DE41H/self-balancing-robot/hardware/schematic/self-balancing-robot/self-balancing-robot.kicad_pcb

## KiCad design Electronic_load_esp32/Electronic_load_esp32.kicad_sch

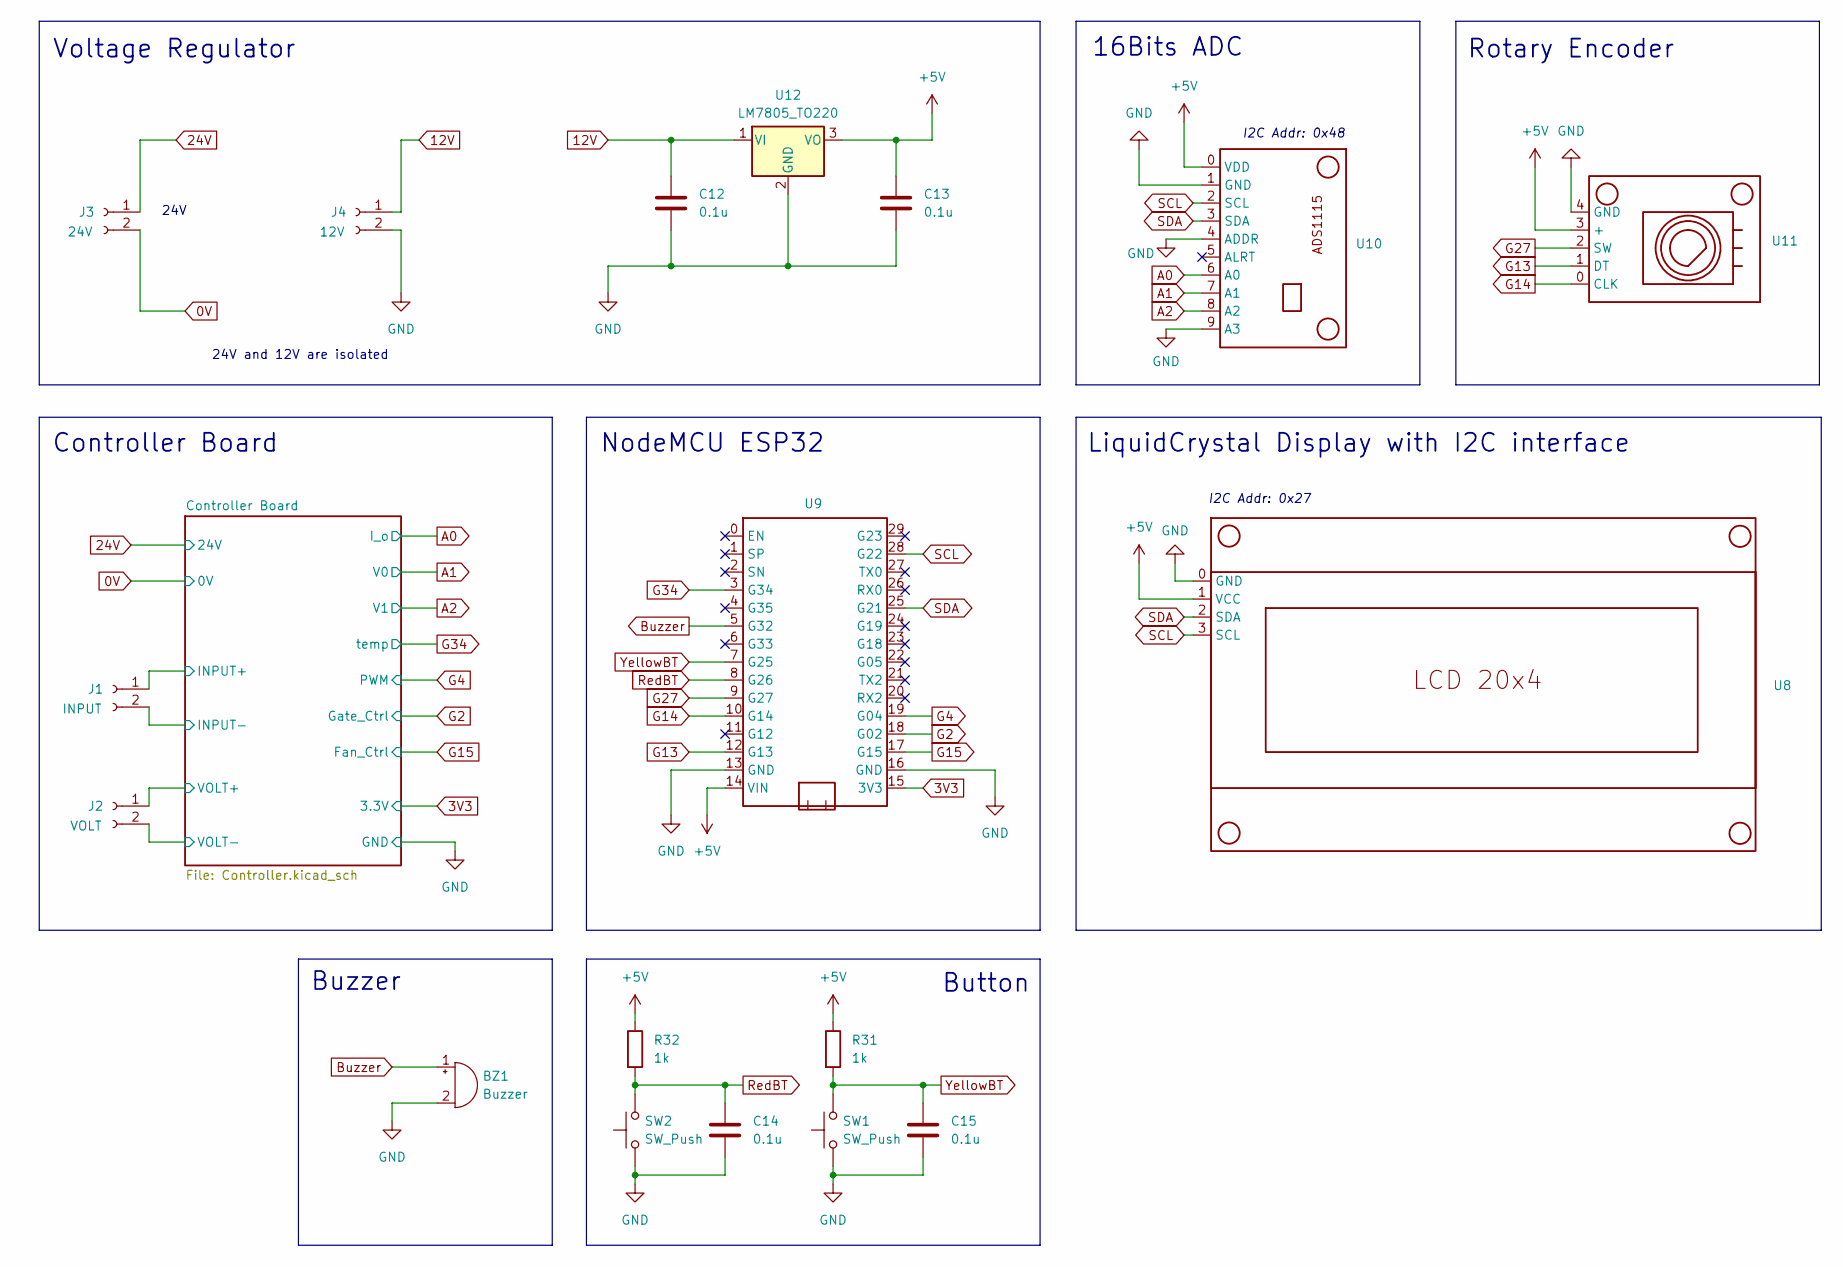
[picture p3: schematic Electronic_load_esp32.kicad_sch]

Parts:
BZ1: Buzzer
C12, C13, C14, C15: 0.1u
J1: INPUT; JST_XA_B02B-XASK-1_1x02_P2.50mm_Vertical
J2: VOLT; JST_XA_B02B-XASK-1_1x02_P2.50mm_Vertical
J3: 24V; JST_XA_B02B-XASK-1_1x02_P2.50mm_Vertical
J4: 12V; JST_XA_B02B-XASK-1_1x02_P2.50mm_Vertical
R31, R32: 1k
SW1, SW2: SW_Push
U8, U10, U11: (no value)
U9: NodeMCU_ESP32_30PIN
U12: LM7805_TO220; TO-220-3_Vertical

Connections:
0V: J3.2
3V3: U9.15 (3V3)
12V: C12.1, J4.1, U12.1 (VI)
24V: J3.1
+5V: C13.1, R31.1, R32.1, U8.1 (VCC), U9.14 (VIN), U10.0 (VDD), U11.3 (+), U12.3 (VO)
A0: U10.6 (A0)
A1: U10.7 (A1)
A2: U10.8 (A2)
Buzzer: BZ1.1 (+), U9.5 (G32)
G2: U9.18 (G02)
G4: U9.19 (G04)
G13: U9.12 (G13), U11.1 (DT)
G14: U9.10 (G14), U11.0 (CLK)
G15: U9.17 (G15)
G27: U9.9 (G27), U11.2 (SW)
G34: U9.3 (G34)
GND: BZ1.2 (-), C12.2, C13.2, C14.2, C15.2, J4.2, SW1.1, SW2.1, U8.0 (GND), U9.13 (GND), U9.16 (GND), U10.1 (GND), U10.4 (ADDR), U10.9 (A3), U11.4 (GND), U12.2 (GND)
INPUT+: J1.1
INPUT-: J1.2
RedBT: C14.1, R32.2, SW2.2, U9.8 (G26)
SCL: U8.3 (SCL), U9.28 (G22), U10.2 (SCL)
SDA: U8.2 (SDA), U9.25 (G21), U10.3 (SDA)
VOLT+: J2.1
VOLT-: J2.2
YellowBT: C15.1, R31.2, SW1.2, U9.7 (G25)

Notes on the sheet:
24V and 12V are isolated
Rotary Encoder
Voltage Regulator
I2C Addr: 0x27
NodeMCU ESP32
Controller Board
24V
I2C Addr: 0x48
Buzzer
16Bits ADC
LiquidCrystal Display with I2C interface
Button
